ShellAlbert/PowerOverFiber/SerialCamera/Core/Inc/main.h

#define CAM1_PWDN_Pin GPIO_PIN_6
#define CAM1_PWDN_GPIO_Port GPIOF
#define LED1_Pin GPIO_PIN_8
#define LED1_GPIO_Port GPIOF
#define LED2_Pin GPIO_PIN_9
#define LED2_GPIO_Port GPIOF
#define CAM1_RST_Pin GPIO_PIN_1
#define CAM1_RST_GPIO_Port GPIOC
#define LD_PWR_EN_Pin GPIO_PIN_5
#define LD_PWR_EN_GPIO_Port GPIOA
#define SYNC_SWITCH_Pin GPIO_PIN_1
#define SYNC_SWITCH_GPIO_Port GPIOB
#define HT_DRDYn_Pin GPIO_PIN_12
#define HT_DRDYn_GPIO_Port GPIOB
#define DAY_NIGHT_Pin GPIO_PIN_8
#define DAY_NIGHT_GPIO_Port GPIOA
#define VER1_Pin GPIO_PIN_15
#define VER1_GPIO_Port GPIOA
#define CAM2_PWR_EN_Pin GPIO_PIN_9
#define CAM2_PWR_EN_GPIO_Port GPIOG
#define CAM1_PWR_EN_Pin GPIO_PIN_10
#define CAM1_PWR_EN_GPIO_Port GPIOG
#define BUS_SWITCH_Pin GPIO_PIN_5
#define BUS_SWITCH_GPIO_Port GPIOB
#define VER2_Pin GPIO_PIN_8
#define VER2_GPIO_Port GPIOB
